AirChandler/pxt-arcade-RPi-smart-shield/cmsis_core/docs/Core/html/CMSIS_TZ_files.png

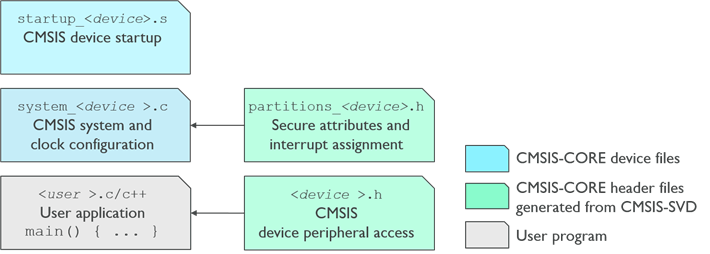
cmsis_core/docs/Core/html/CMSIS_TZ_files.png
