AirChandler/pxt-arcade-RPi-smart-shield/cmsis_core/docs/Core/html/SimpleUseCase.png

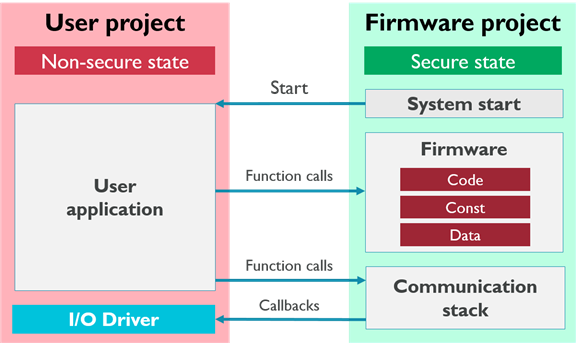
cmsis_core/docs/Core/html/SimpleUseCase.png
