AirChandler/pxt-arcade-RPi-smart-shield/cmsis_core/docs/DAP/html/CMSIS_DAP_SWStack.png

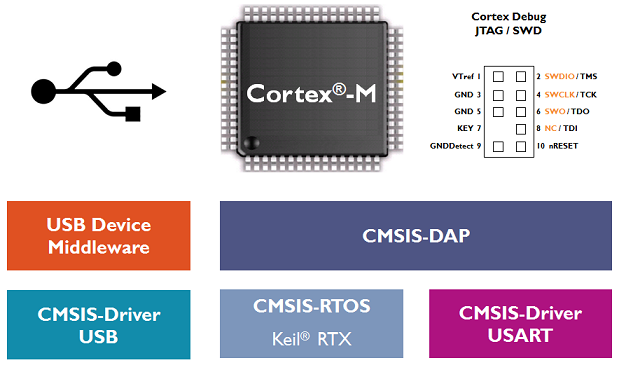
cmsis_core/docs/DAP/html/CMSIS_DAP_SWStack.png
