AirChandler/pxt-arcade-RPi-smart-shield/cmsis_core/docs/DAP/html/MDK_Flash.png

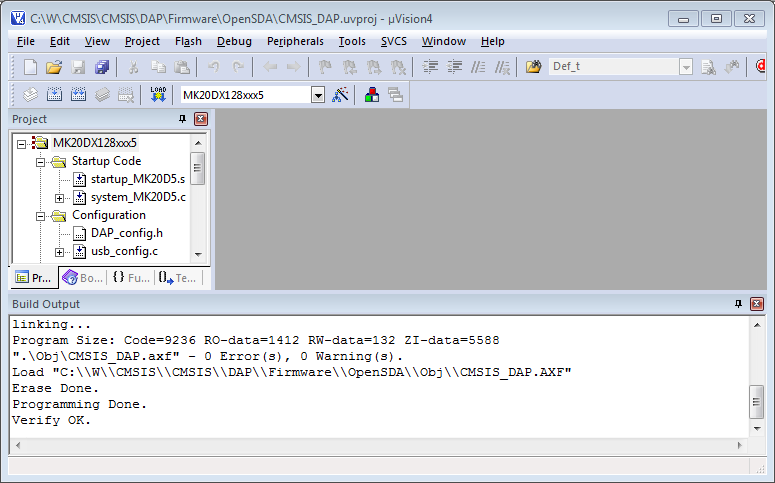
cmsis_core/docs/DAP/html/MDK_Flash.png
