AirChandler/pxt-arcade-RPi-smart-shield/cmsis_core/docs/DAP/html/RTE.png

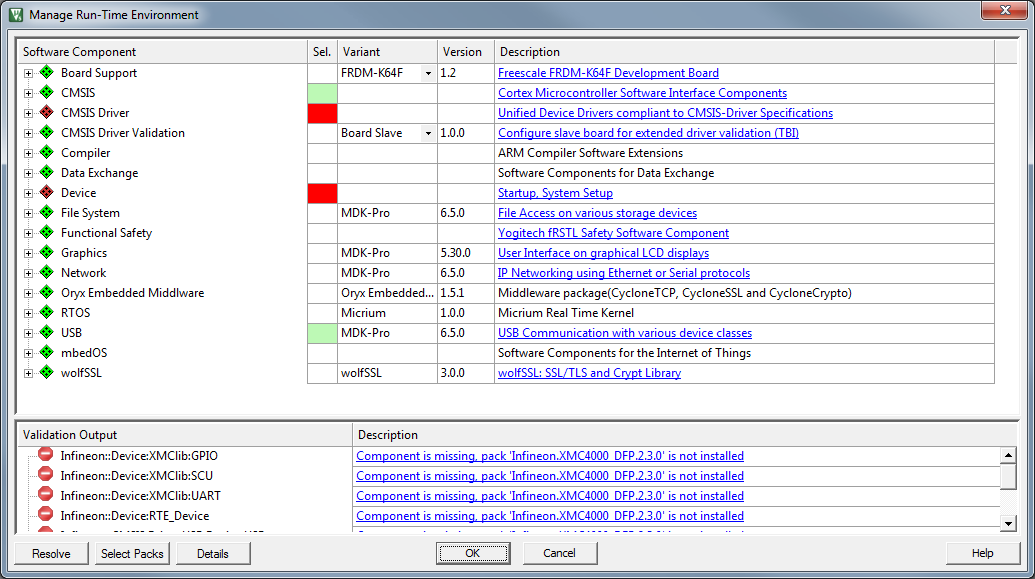
cmsis_core/docs/DAP/html/RTE.png
