AirChandler/pxt-arcade-RPi-smart-shield/cmsis_core/docs/Driver/html/driver_sai_i2s.png

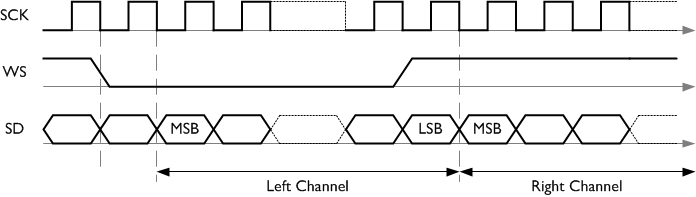
cmsis_core/docs/Driver/html/driver_sai_i2s.png
