AirChandler/pxt-arcade-RPi-smart-shield/cmsis_core/docs/Driver/html/I2C_BlockDiagram.png

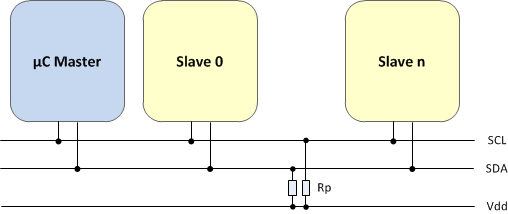
cmsis_core/docs/Driver/html/I2C_BlockDiagram.png
