AirChandler/pxt-arcade-RPi-smart-shield/cmsis_core/docs/Driver/html/msc_inline_mscgraph_2.png

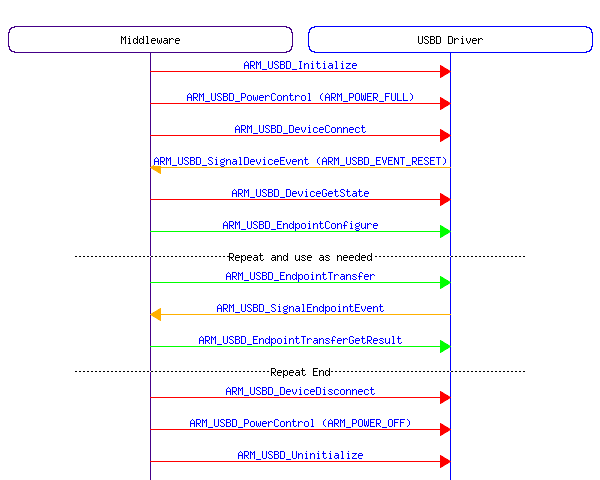
cmsis_core/docs/Driver/html/msc_inline_mscgraph_2.png
