AirChandler/pxt-arcade-RPi-smart-shield/cmsis_core/docs/Driver/html/NAND_Schematics.png

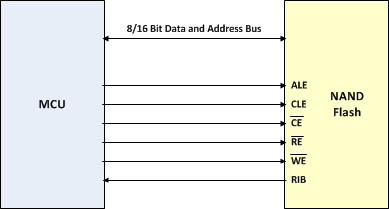
cmsis_core/docs/Driver/html/NAND_Schematics.png
