AirChandler/pxt-arcade-RPi-smart-shield/cmsis_core/docs/Driver/html/Non_blocking_transmit_small.png

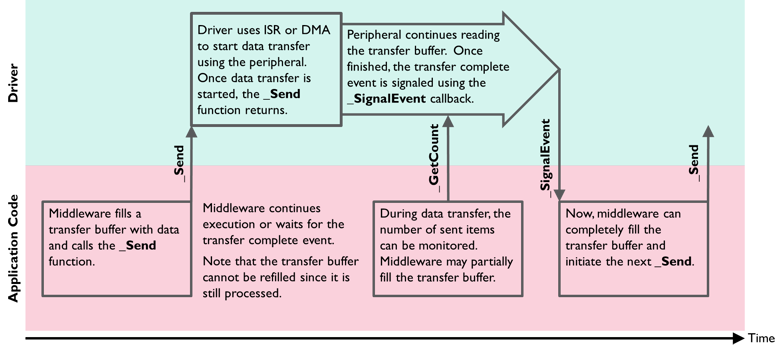
cmsis_core/docs/Driver/html/Non_blocking_transmit_small.png
