AirChandler/pxt-arcade-RPi-smart-shield/cmsis_core/docs/Driver/html/SAI_Schematics.png

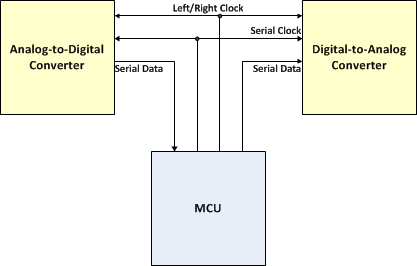
cmsis_core/docs/Driver/html/SAI_Schematics.png
