AirChandler/pxt-arcade-RPi-smart-shield/cmsis_core/docs/Driver/html/SD_4BitBusMode.png

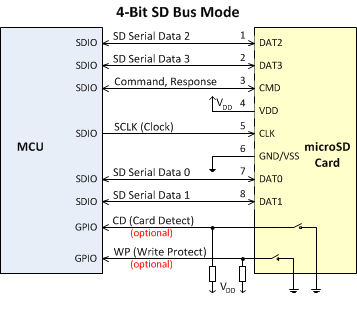
cmsis_core/docs/Driver/html/SD_4BitBusMode.png
