AirChandler/pxt-arcade-RPi-smart-shield/cmsis_core/docs/Driver/html/SPI_BusMode.png

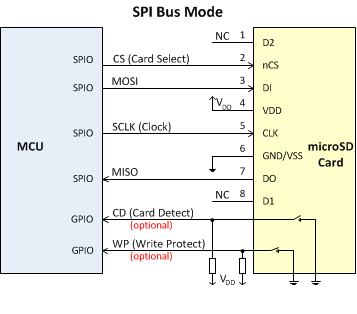
cmsis_core/docs/Driver/html/SPI_BusMode.png
