AirChandler/pxt-arcade-RPi-smart-shield/cmsis_core/docs/Driver/html/SPI_Master3Slaves.png

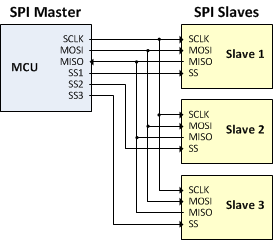
cmsis_core/docs/Driver/html/SPI_Master3Slaves.png
