AirChandler/pxt-arcade-RPi-smart-shield/cmsis_core/docs/Driver/html/storage_sw_stack.png

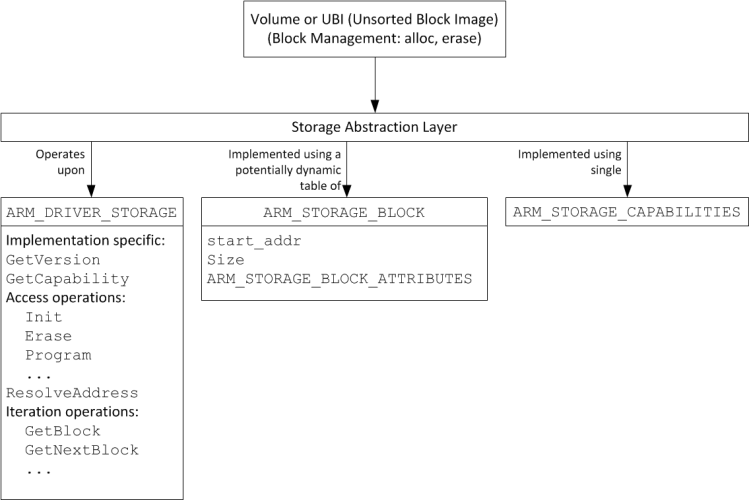
cmsis_core/docs/Driver/html/storage_sw_stack.png
