AirChandler/pxt-arcade-RPi-smart-shield/cmsis_core/docs/Driver/html/USB_Schematics.png

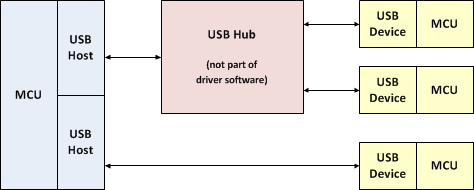
cmsis_core/docs/Driver/html/USB_Schematics.png
