AirChandler/pxt-arcade-RPi-smart-shield/cmsis_core/docs/Driver/html/WiFi.png

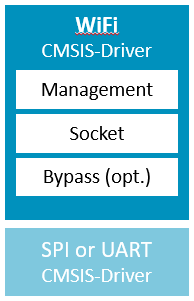
cmsis_core/docs/Driver/html/WiFi.png
