AirChandler/pxt-arcade-RPi-smart-shield/cmsis_core/docs/DSP/html/Biquad.gif

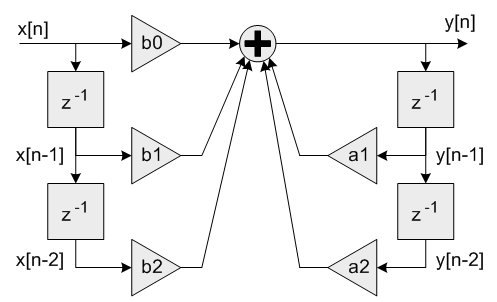
cmsis_core/docs/DSP/html/Biquad.gif
