AirChandler/pxt-arcade-RPi-smart-shield/cmsis_core/docs/DSP/html/BiquadPostshift.gif

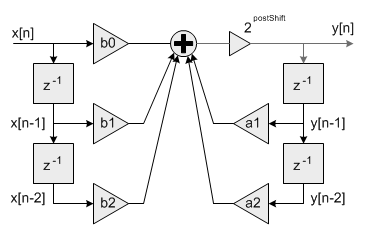
cmsis_core/docs/DSP/html/BiquadPostshift.gif
