AirChandler/pxt-arcade-RPi-smart-shield/cmsis_core/docs/DSP/html/FFTBinInput.gif

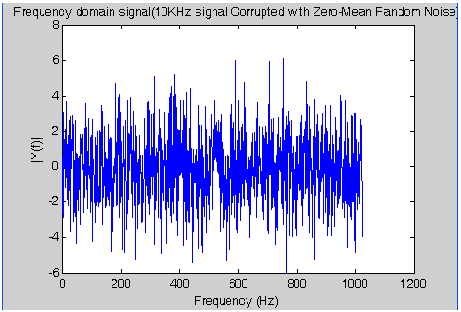
cmsis_core/docs/DSP/html/FFTBinInput.gif
