AirChandler/pxt-arcade-RPi-smart-shield/cmsis_core/docs/DSP/html/FIRLPF_coeffs.gif

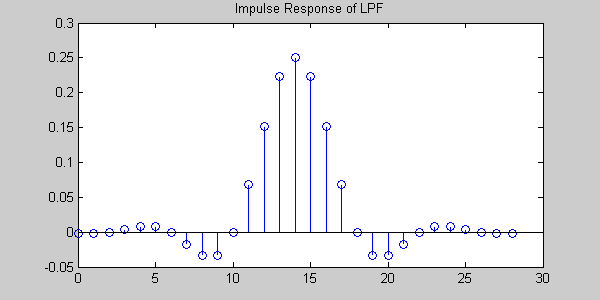
cmsis_core/docs/DSP/html/FIRLPF_coeffs.gif
