AirChandler/pxt-arcade-RPi-smart-shield/cmsis_core/docs/DSP/html/FIRLPF_output.gif

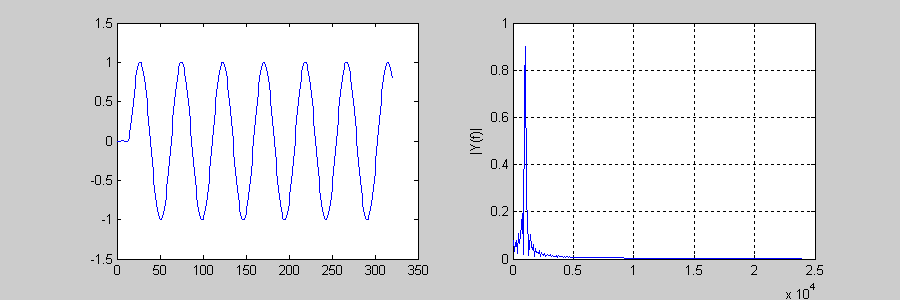
cmsis_core/docs/DSP/html/FIRLPF_output.gif
