AirChandler/pxt-arcade-RPi-smart-shield/cmsis_core/docs/DSP/html/FIRLPF_response.gif

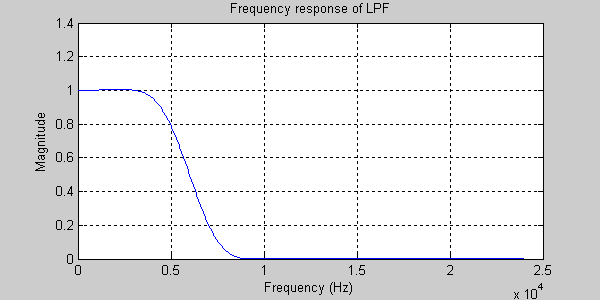
cmsis_core/docs/DSP/html/FIRLPF_response.gif
