AirChandler/pxt-arcade-RPi-smart-shield/cmsis_core/docs/DSP/html/GEQ_allbandresponse.gif

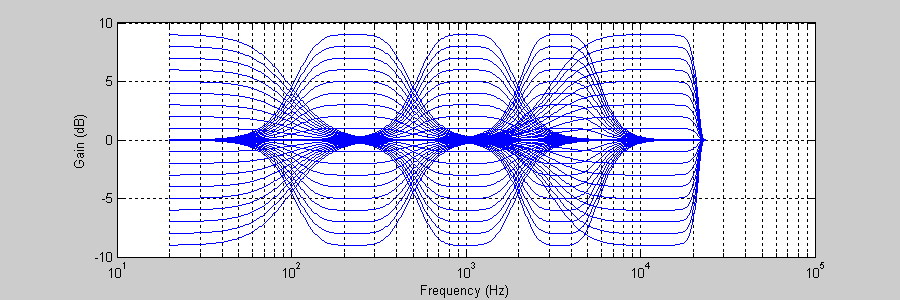
cmsis_core/docs/DSP/html/GEQ_allbandresponse.gif
