AirChandler/pxt-arcade-RPi-smart-shield/cmsis_core/docs/DSP/html/GEQ_bandresponse.gif

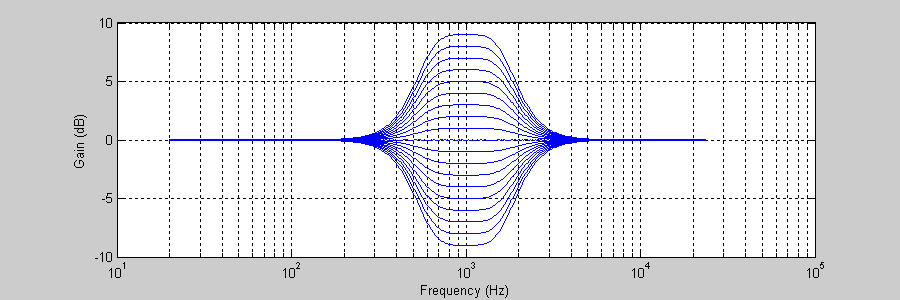
cmsis_core/docs/DSP/html/GEQ_bandresponse.gif
