AirChandler/pxt-arcade-RPi-smart-shield/cmsis_core/docs/DSP/html/IIRLattice.gif

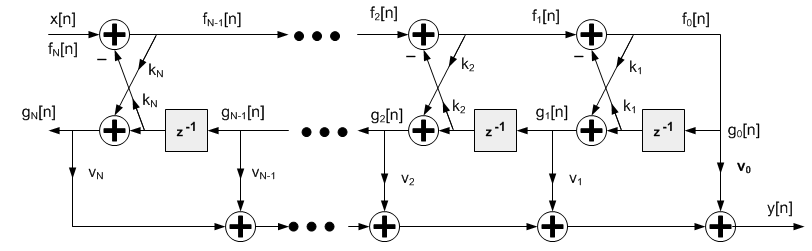
cmsis_core/docs/DSP/html/IIRLattice.gif
