AirChandler/pxt-arcade-RPi-smart-shield/cmsis_core/docs/DSP/html/MatrixInverse.gif

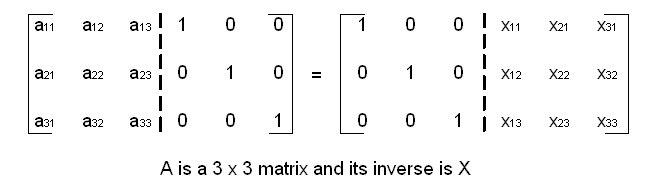
cmsis_core/docs/DSP/html/MatrixInverse.gif
