AirChandler/pxt-arcade-RPi-smart-shield/cmsis_core/docs/DSP/html/park.gif

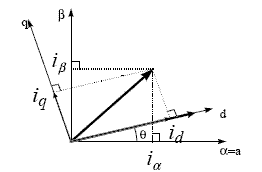
cmsis_core/docs/DSP/html/park.gif
