AirChandler/pxt-arcade-RPi-smart-shield/cmsis_core/docs/DSP/html/RFFTQ15.gif

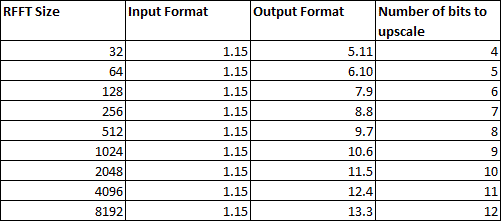
cmsis_core/docs/DSP/html/RFFTQ15.gif
