AirChandler/pxt-arcade-RPi-smart-shield/cmsis_core/docs/DSP/html/Variance.gif

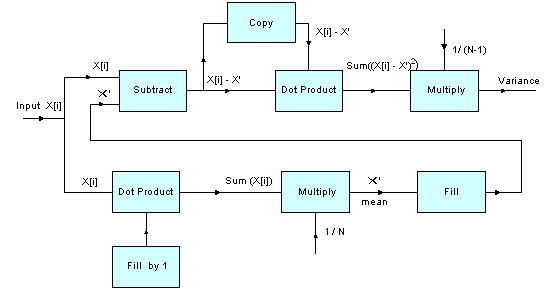
cmsis_core/docs/DSP/html/Variance.gif
