AirChandler/pxt-arcade-RPi-smart-shield/cmsis_core/docs/NN/html/CIFAR10_CNN.gif

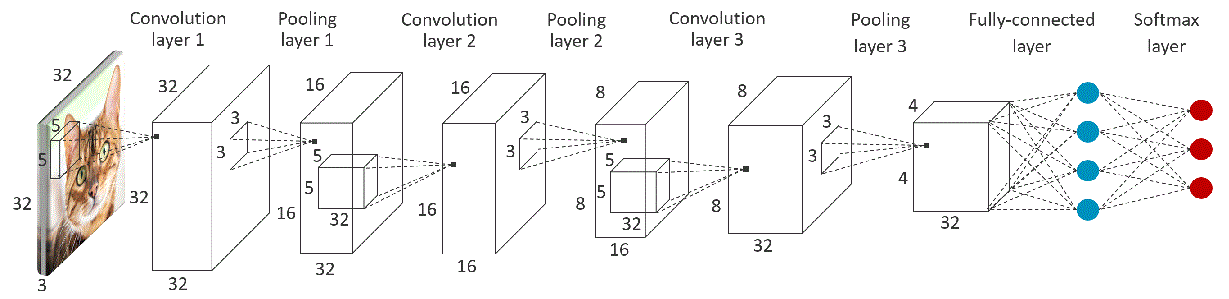
cmsis_core/docs/NN/html/CIFAR10_CNN.gif
