AirChandler/pxt-arcade-RPi-smart-shield/cmsis_core/docs/NN/html/GRU.gif

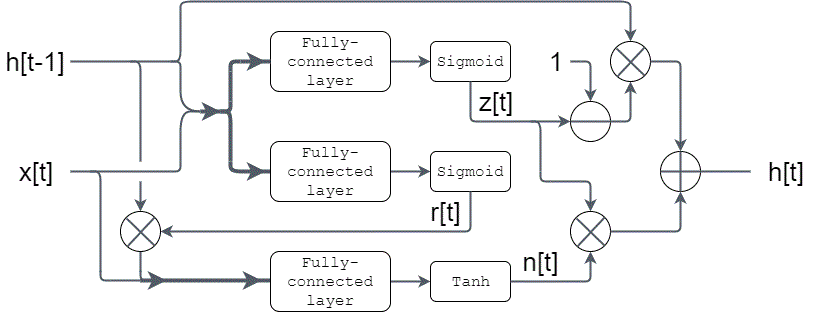
cmsis_core/docs/NN/html/GRU.gif
