AirChandler/pxt-arcade-RPi-smart-shield/cmsis_core/docs/Pack/html/api.png

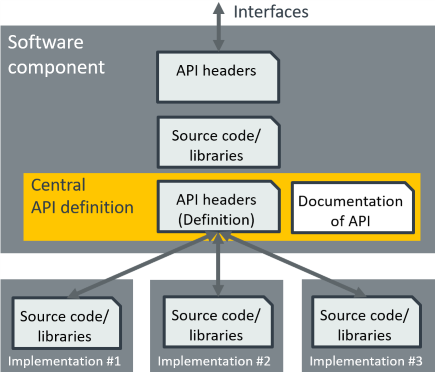
cmsis_core/docs/Pack/html/api.png
