AirChandler/pxt-arcade-RPi-smart-shield/cmsis_core/docs/Pack/html/BSPBundleDisplay.png

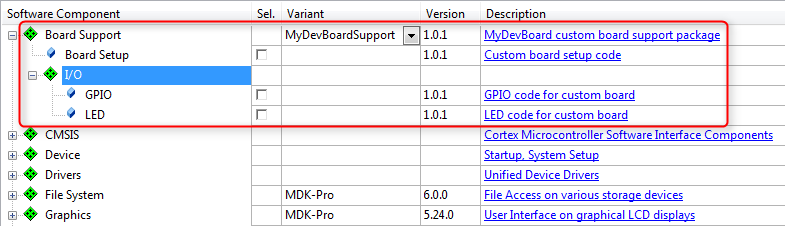
cmsis_core/docs/Pack/html/BSPBundleDisplay.png
