AirChandler/pxt-arcade-RPi-smart-shield/cmsis_core/docs/Pack/html/ConditionsDisplay.png

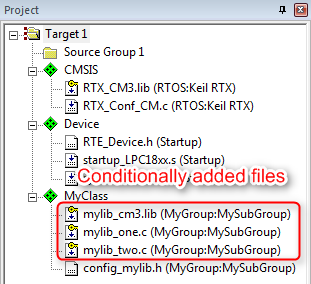
cmsis_core/docs/Pack/html/ConditionsDisplay.png
