AirChandler/pxt-arcade-RPi-smart-shield/cmsis_core/docs/Pack/html/DFPFlow.png

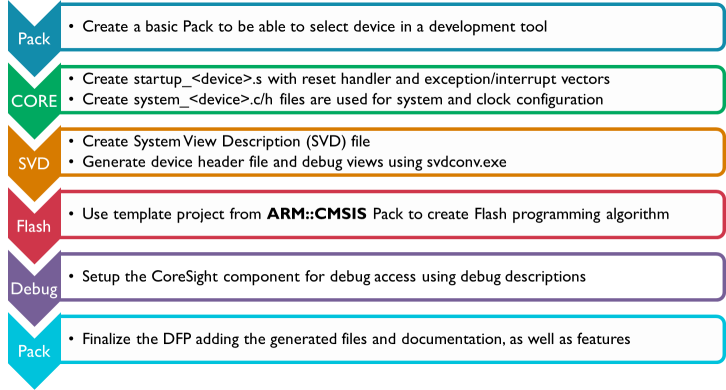
cmsis_core/docs/Pack/html/DFPFlow.png
