AirChandler/pxt-arcade-RPi-smart-shield/cmsis_core/docs/Pack/html/ExampleDisplay.png

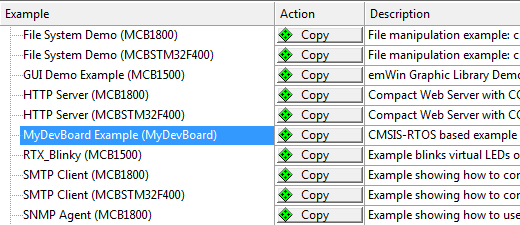
cmsis_core/docs/Pack/html/ExampleDisplay.png
