AirChandler/pxt-arcade-RPi-smart-shield/cmsis_core/docs/Pack/html/FlashProgram.png

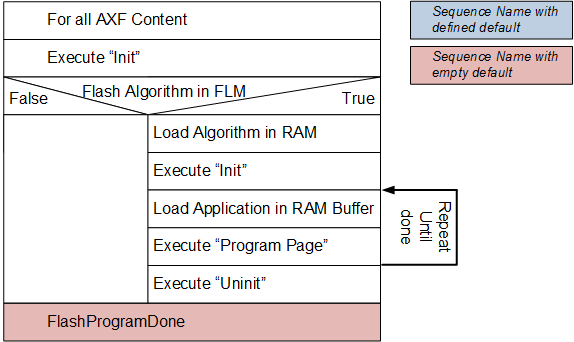
cmsis_core/docs/Pack/html/FlashProgram.png
