AirChandler/pxt-arcade-RPi-smart-shield/cmsis_core/docs/Pack/html/FPATargetOptions.png

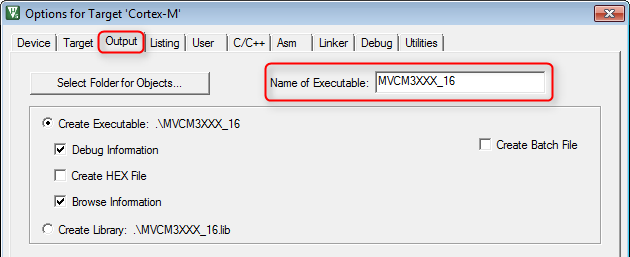
cmsis_core/docs/Pack/html/FPATargetOptions.png
