AirChandler/pxt-arcade-RPi-smart-shield/cmsis_core/docs/Pack/html/MVCM3SpecTable.png

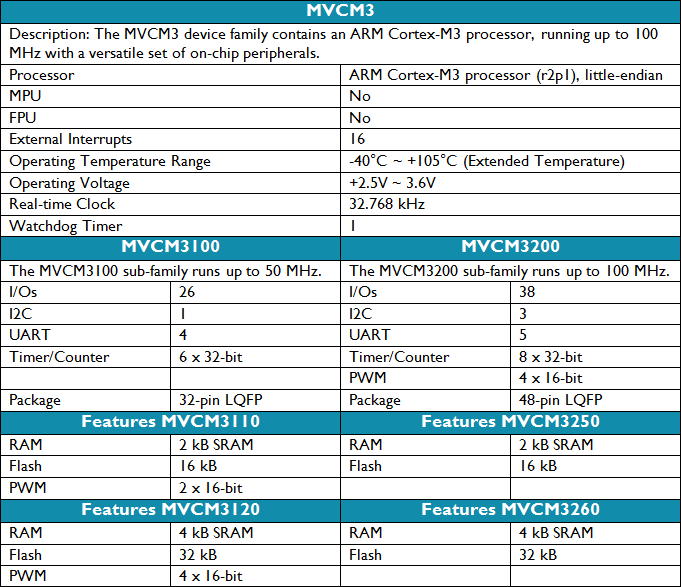
cmsis_core/docs/Pack/html/MVCM3SpecTable.png
