AirChandler/pxt-arcade-RPi-smart-shield/cmsis_core/docs/Pack/html/PDSC_Example_top.png

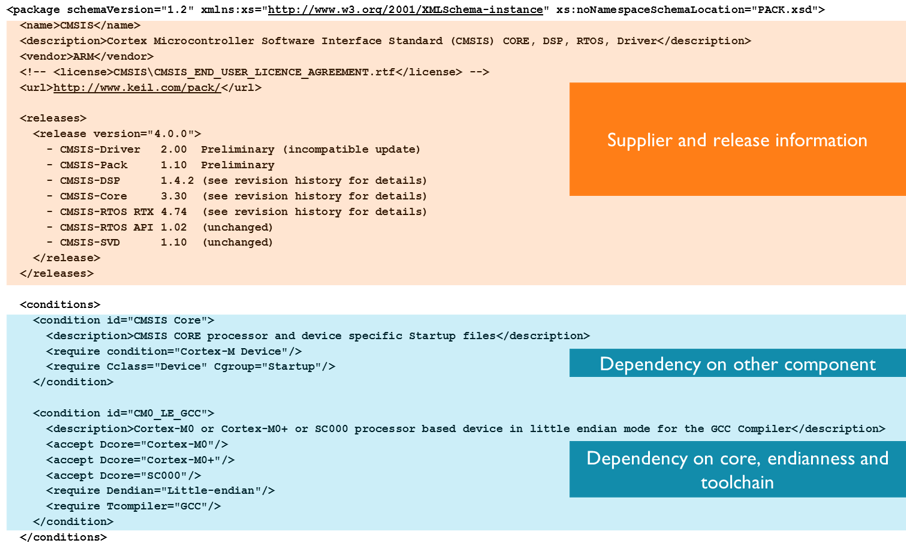
cmsis_core/docs/Pack/html/PDSC_Example_top.png
