AirChandler/pxt-arcade-RPi-smart-shield/cmsis_core/docs/Pack/html/Reset.png

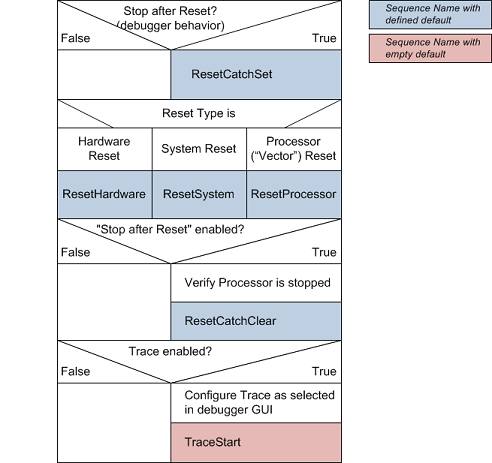
cmsis_core/docs/Pack/html/Reset.png
