AirChandler/pxt-arcade-RPi-smart-shield/cmsis_core/docs/Pack/html/StartupSystemFilesAdded.png

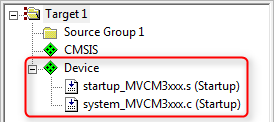
cmsis_core/docs/Pack/html/StartupSystemFilesAdded.png
