AirChandler/pxt-arcade-RPi-smart-shield/cmsis_core/docs/Pack/html/SVDIncluded.png

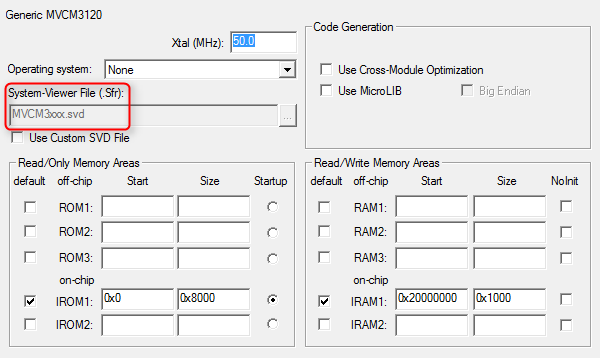
cmsis_core/docs/Pack/html/SVDIncluded.png
