AirChandler/pxt-arcade-RPi-smart-shield/cmsis_core/docs/Pack/html/VariantDisplay.png

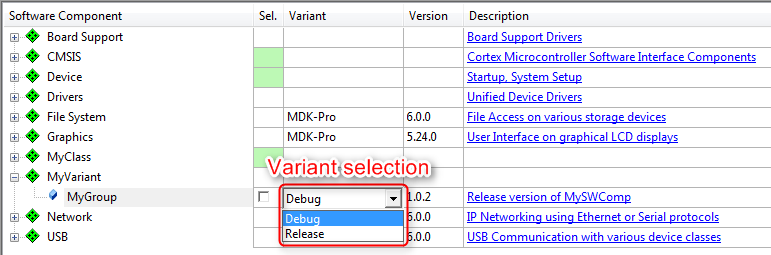
cmsis_core/docs/Pack/html/VariantDisplay.png
