AirChandler/pxt-arcade-RPi-smart-shield/cmsis_core/docs/RTOS2/html/config_wizard.png

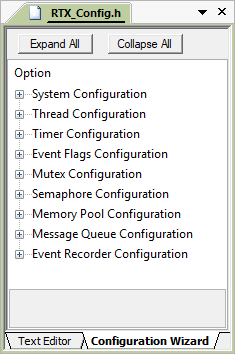
cmsis_core/docs/RTOS2/html/config_wizard.png
