AirChandler/pxt-arcade-RPi-smart-shield/cmsis_core/docs/RTOS2/html/manage_rte_output.png

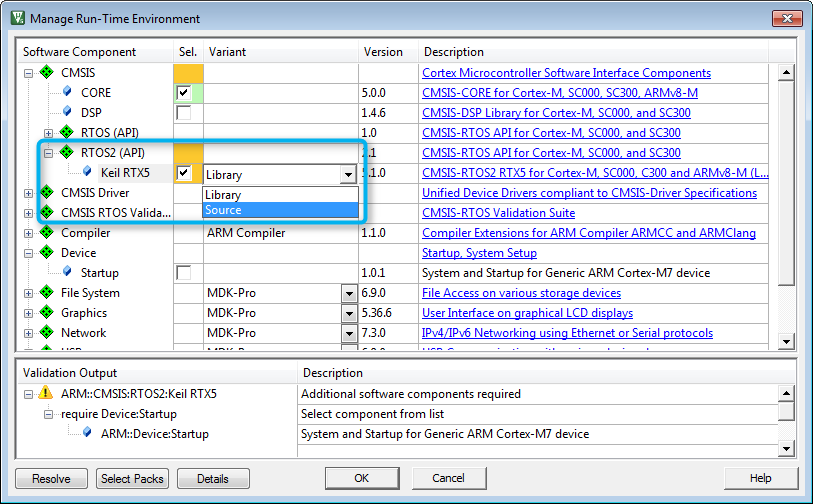
cmsis_core/docs/RTOS2/html/manage_rte_output.png
