AirChandler/pxt-arcade-RPi-smart-shield/cmsis_core/docs/RTOS2/html/MemAllocGlob.png

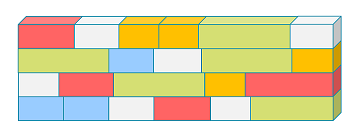
cmsis_core/docs/RTOS2/html/MemAllocGlob.png
