AirChandler/pxt-arcade-RPi-smart-shield/cmsis_core/docs/RTOS2/html/PC-Lint.png

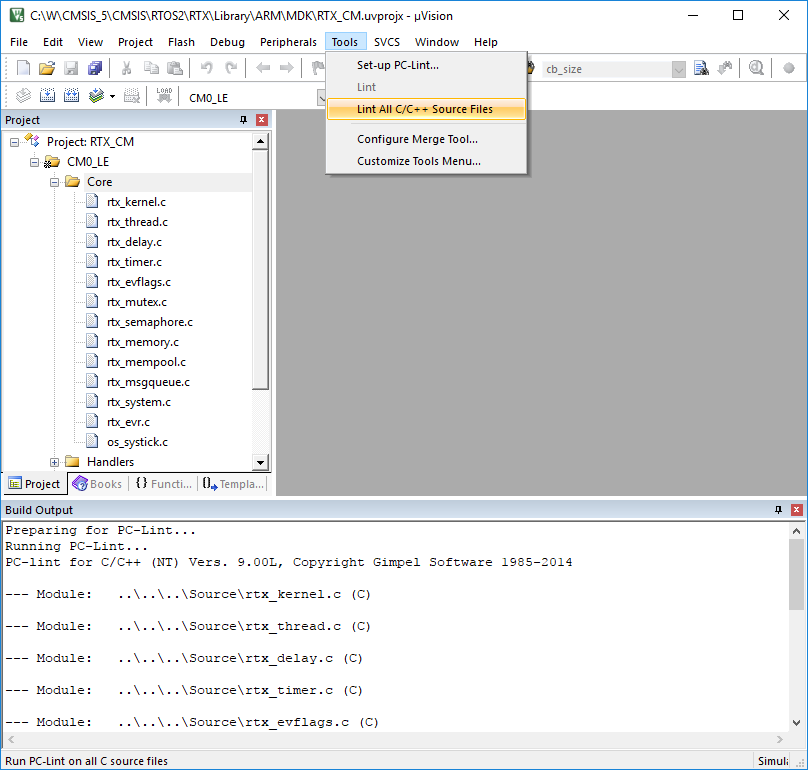
cmsis_core/docs/RTOS2/html/PC-Lint.png
