AirChandler/pxt-arcade-RPi-smart-shield/cmsis_core/docs/RTOS2/html/project_window.png

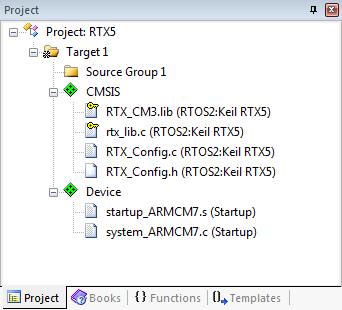
cmsis_core/docs/RTOS2/html/project_window.png
