AirChandler/pxt-arcade-RPi-smart-shield/cmsis_core/docs/RTOS2/html/simple_signal.png

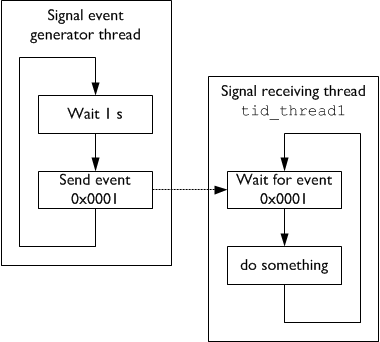
cmsis_core/docs/RTOS2/html/simple_signal.png
