AirChandler/pxt-arcade-RPi-smart-shield/cmsis_core/docs/RTOS/html/API_Structure.png

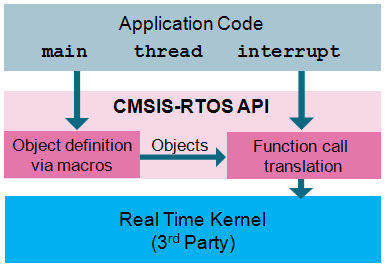
cmsis_core/docs/RTOS/html/API_Structure.png
