AirChandler/pxt-arcade-RPi-smart-shield/cmsis_core/docs/RTOS/html/CMSIS_RTOS_Files.png

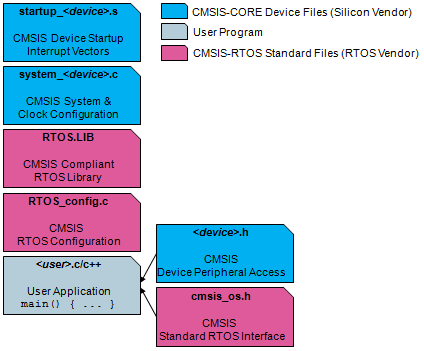
cmsis_core/docs/RTOS/html/CMSIS_RTOS_Files.png
