AirChandler/pxt-arcade-RPi-smart-shield/cmsis_core/docs/RTOS/html/config_wizard.png

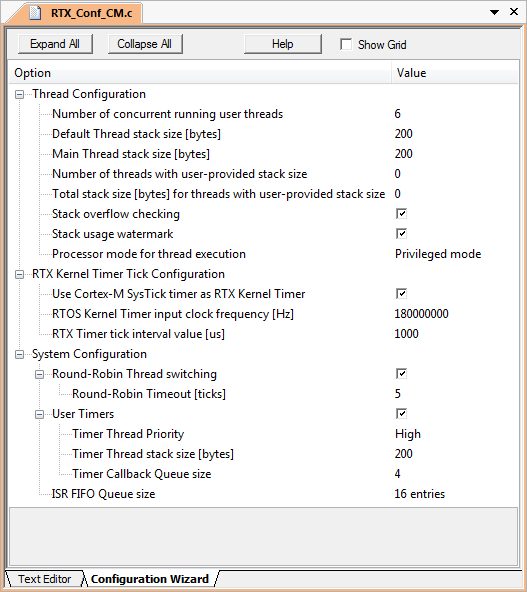
cmsis_core/docs/RTOS/html/config_wizard.png
