AirChandler/pxt-arcade-RPi-smart-shield/cmsis_core/docs/SVD/html/CMSIS_SVD_Schema_Gen.png

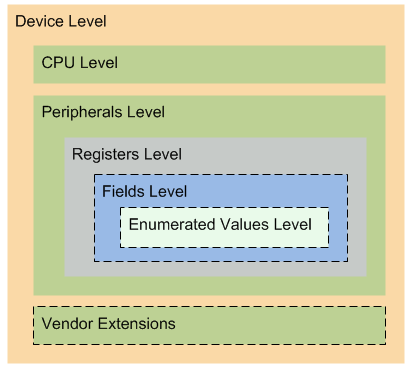
cmsis_core/docs/SVD/html/CMSIS_SVD_Schema_Gen.png
