AirChandler/pxt-arcade-RPi-smart-shield/cmsis_core/docs/Zone/html/AddMemoryBlock.png

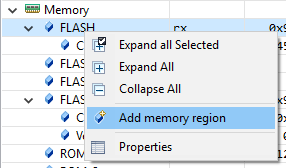
cmsis_core/docs/Zone/html/AddMemoryBlock.png
