AirChandler/pxt-arcade-RPi-smart-shield/cmsis_core/docs/Zone/html/DelMemoryRegion.png

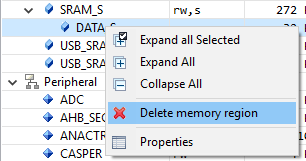
cmsis_core/docs/Zone/html/DelMemoryRegion.png
