AirChandler/pxt-arcade-RPi-smart-shield/cmsis_core/docs/Zone/html/hello_world_output.png

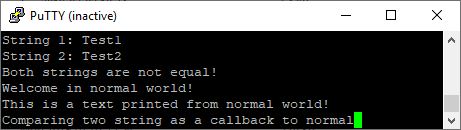
cmsis_core/docs/Zone/html/hello_world_output.png
