AirChandler/pxt-arcade-RPi-smart-shield/cmsis_core/docs/Zone/html/import_from_file.png

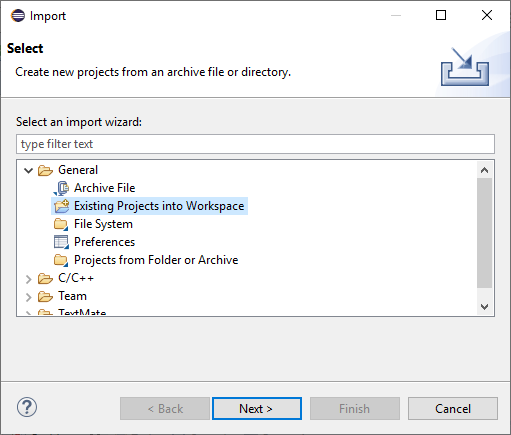
cmsis_core/docs/Zone/html/import_from_file.png
