AirChandler/pxt-arcade-RPi-smart-shield/cmsis_core/docs/Zone/html/import_projects.png

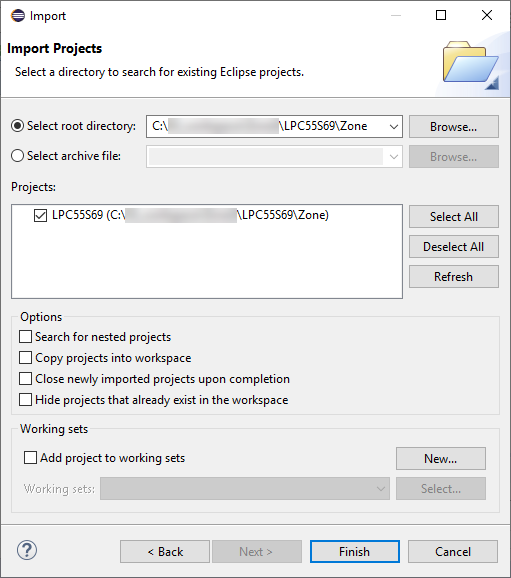
cmsis_core/docs/Zone/html/import_projects.png
