AirChandler/pxt-arcade-RPi-smart-shield/cmsis_core/docs/Zone/html/lpc55_resource_map.png

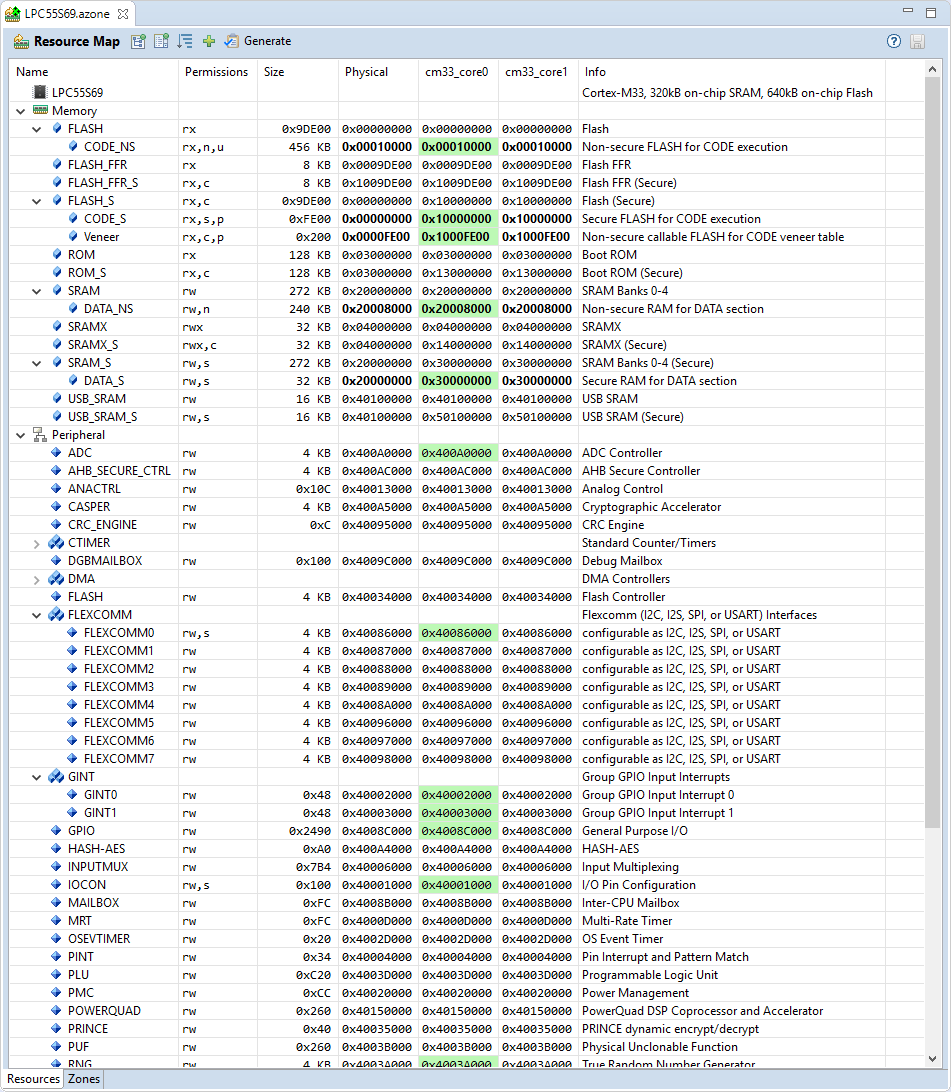
cmsis_core/docs/Zone/html/lpc55_resource_map.png
