AirChandler/pxt-arcade-RPi-smart-shield/cmsis_core/docs/Zone/html/lpc55_system_startup.png

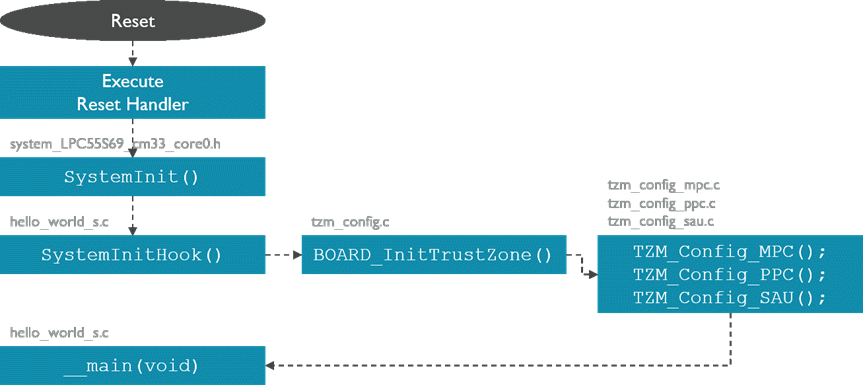
cmsis_core/docs/Zone/html/lpc55_system_startup.png
