AirChandler/pxt-arcade-RPi-smart-shield/cmsis_core/docs/Zone/html/mpu.png

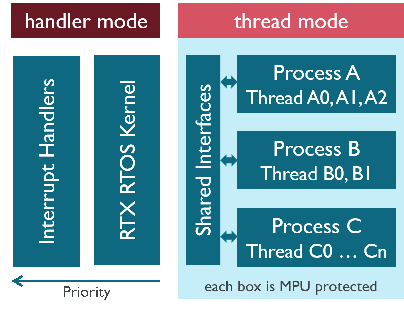
cmsis_core/docs/Zone/html/mpu.png
