AirChandler/pxt-arcade-RPi-smart-shield/cmsis_core/docs/Zone/html/NewZoneCM33_0.png

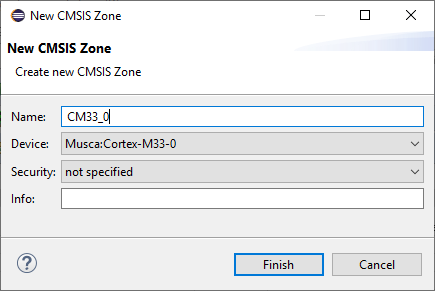
cmsis_core/docs/Zone/html/NewZoneCM33_0.png
