AirChandler/pxt-arcade-RPi-smart-shield/cmsis_core/docs/Zone/html/Partitioning_Hardware.png

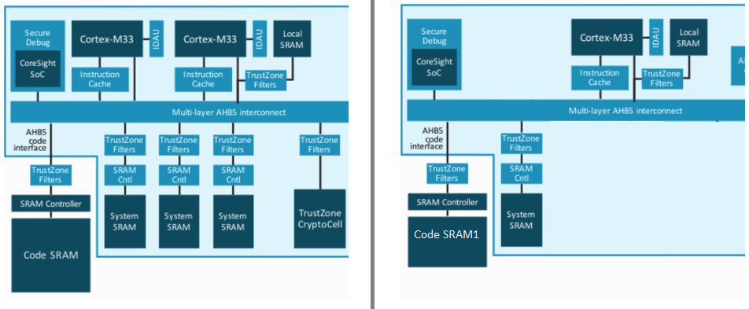
cmsis_core/docs/Zone/html/Partitioning_Hardware.png
