AirChandler/pxt-arcade-RPi-smart-shield/cmsis_core/docs/Zone/html/Partitioning_Workflow.png

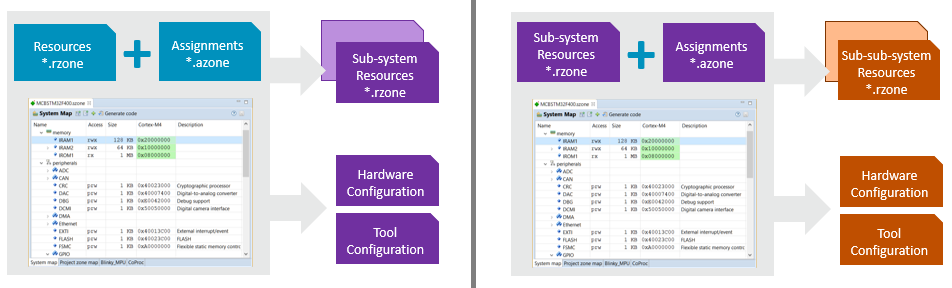
cmsis_core/docs/Zone/html/Partitioning_Workflow.png
