AirChandler/pxt-arcade-RPi-smart-shield/cmsis_core/docs/Zone/html/peripheral_properties.png

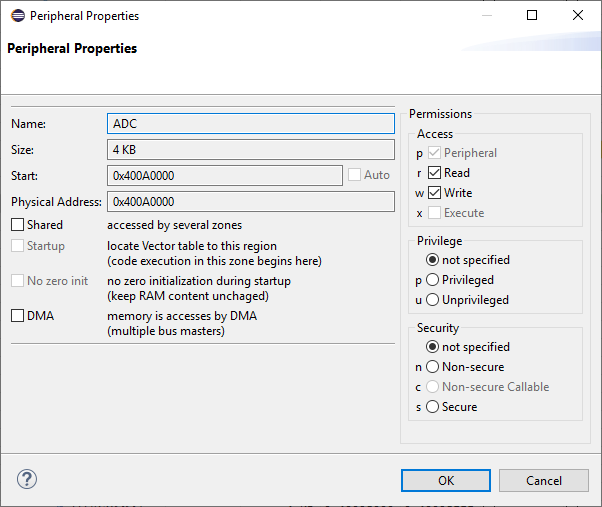
cmsis_core/docs/Zone/html/peripheral_properties.png
