AirChandler/pxt-arcade-RPi-smart-shield/cmsis_core/docs/Zone/html/res_prop.png

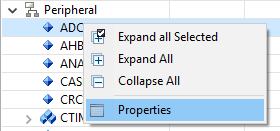
cmsis_core/docs/Zone/html/res_prop.png
