AirChandler/pxt-arcade-RPi-smart-shield/cmsis_core/docs/Zone/html/SpecifyRzoneFile.png

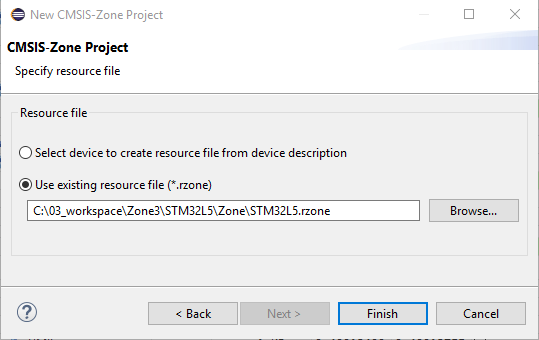
cmsis_core/docs/Zone/html/SpecifyRzoneFile.png
