AirChandler/pxt-arcade-RPi-smart-shield/cmsis_core/docs/Zone/html/STM32L5_zones.png

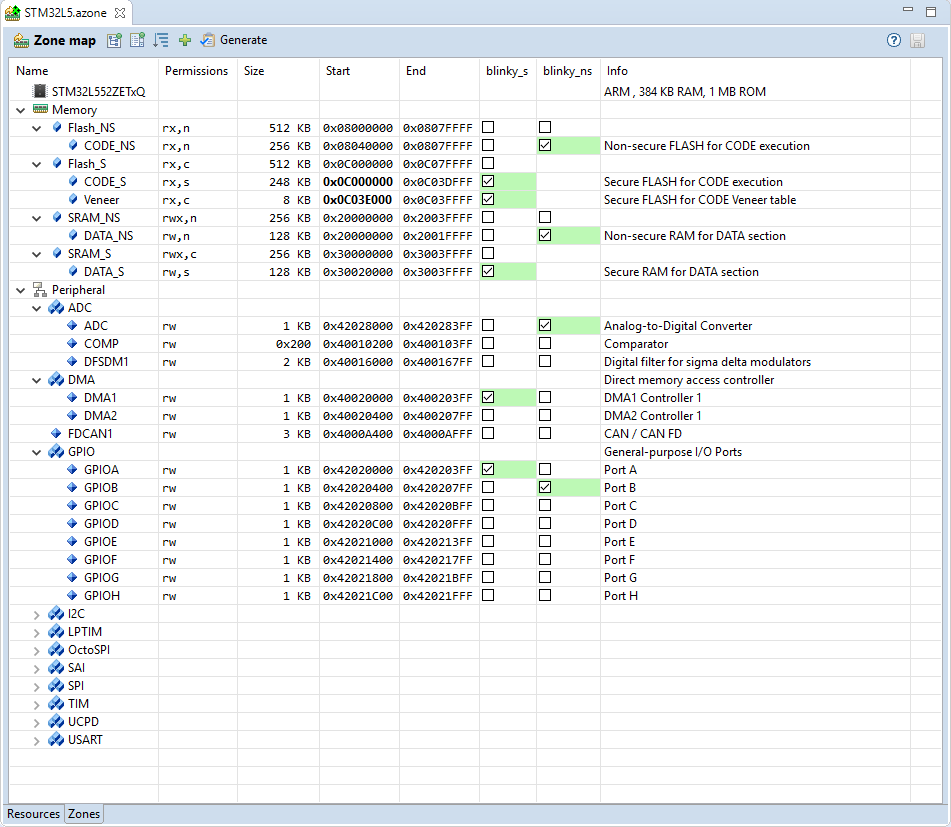
cmsis_core/docs/Zone/html/STM32L5_zones.png
