AirChandler/pxt-arcade-RPi-smart-shield/cmsis_core/docs/Zone/html/zone_map.png

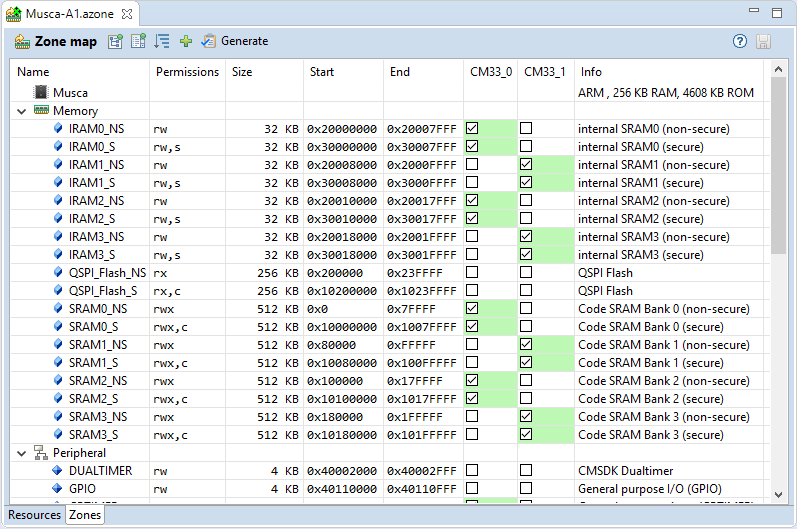
cmsis_core/docs/Zone/html/zone_map.png
