AirChandler/pxt-arcade-RPi-smart-shield/jacdac-c/jacdac/spec/images/jacdac-proto-timings.png

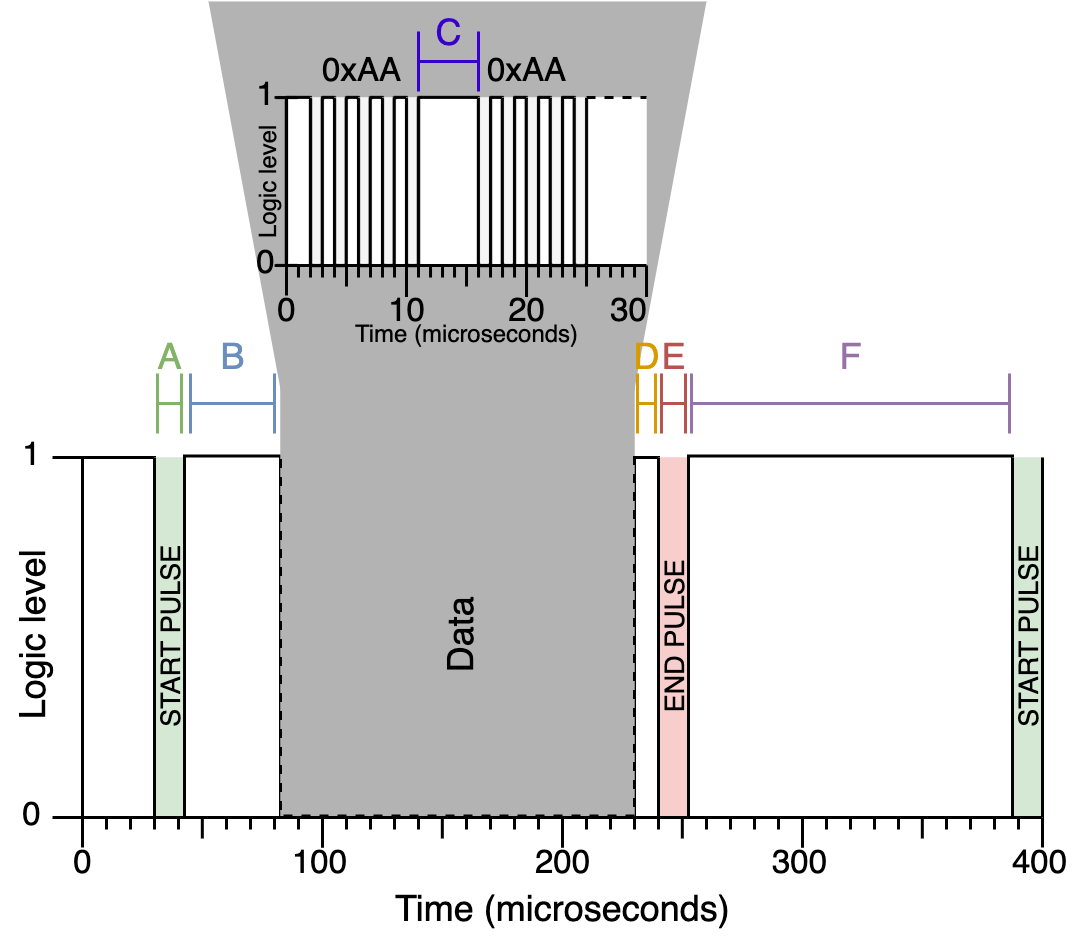
jacdac-c/jacdac/spec/images/jacdac-proto-timings.png
