AirChandler/pxt-arcade-RPi-smart-shield/jacdac-c/jacdac/spec/images/jacdac-stack-no-trans.png

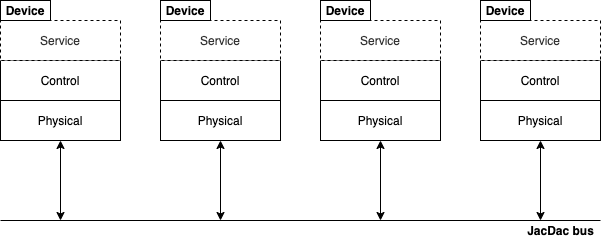
jacdac-c/jacdac/spec/images/jacdac-stack-no-trans.png
