AirChandler/pxt-arcade-RPi-smart-shield/jacdac-c/jacdac/spec/images/jacdac-state-diagram.png

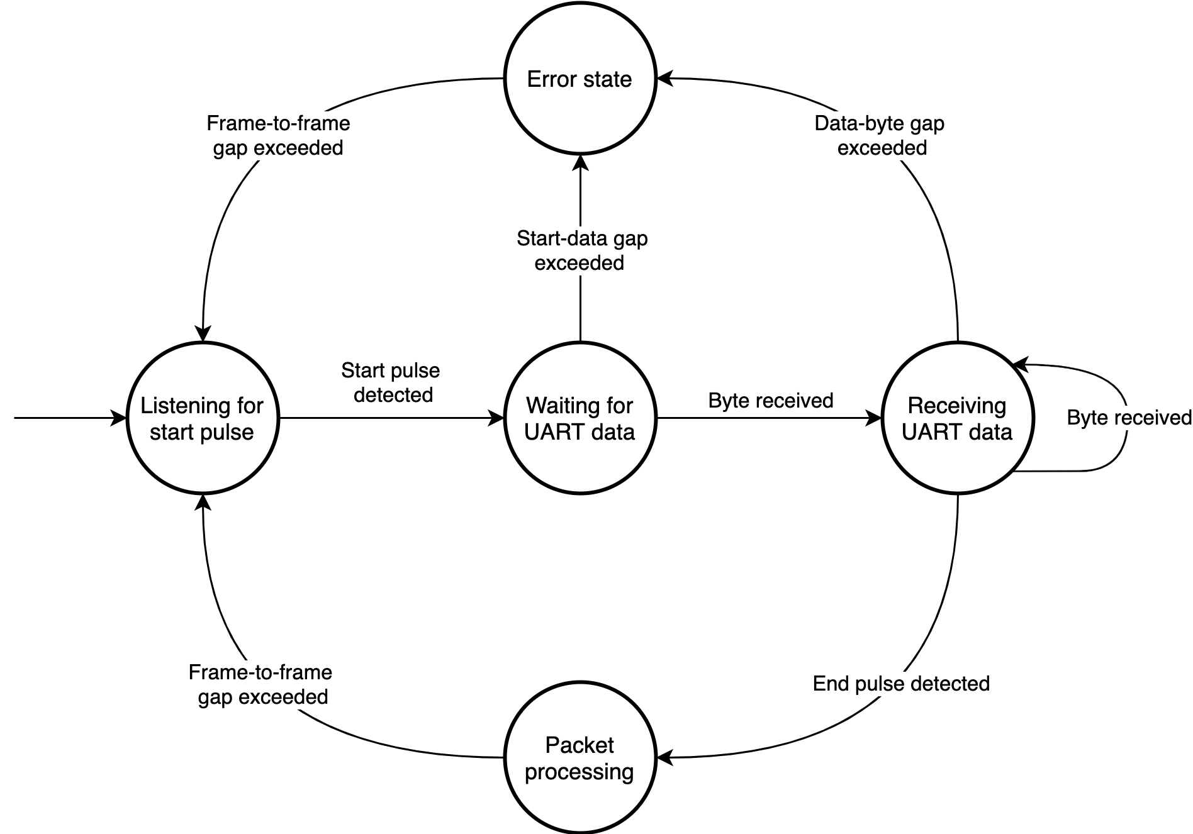
jacdac-c/jacdac/spec/images/jacdac-state-diagram.png
