AirChandler/pxt-arcade-RPi-smart-shield/cmsis_core/docs/Pack/html/component_files.png

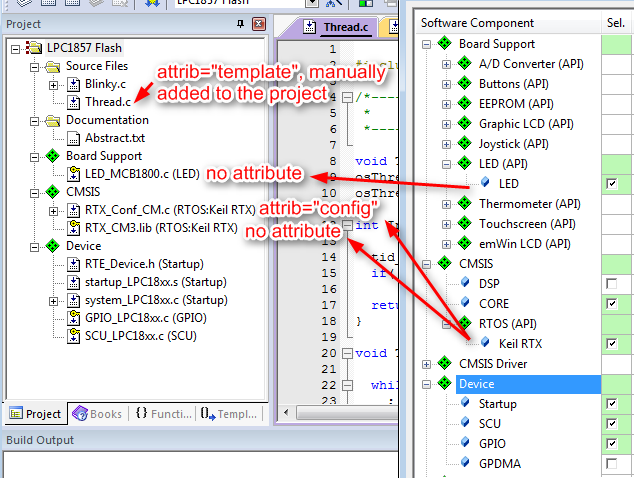
cmsis_core/docs/Pack/html/component_files.png
