AirChandler/pxt-arcade-RPi-smart-shield/cmsis_core/docs/Pack/html/Component_Instances.png

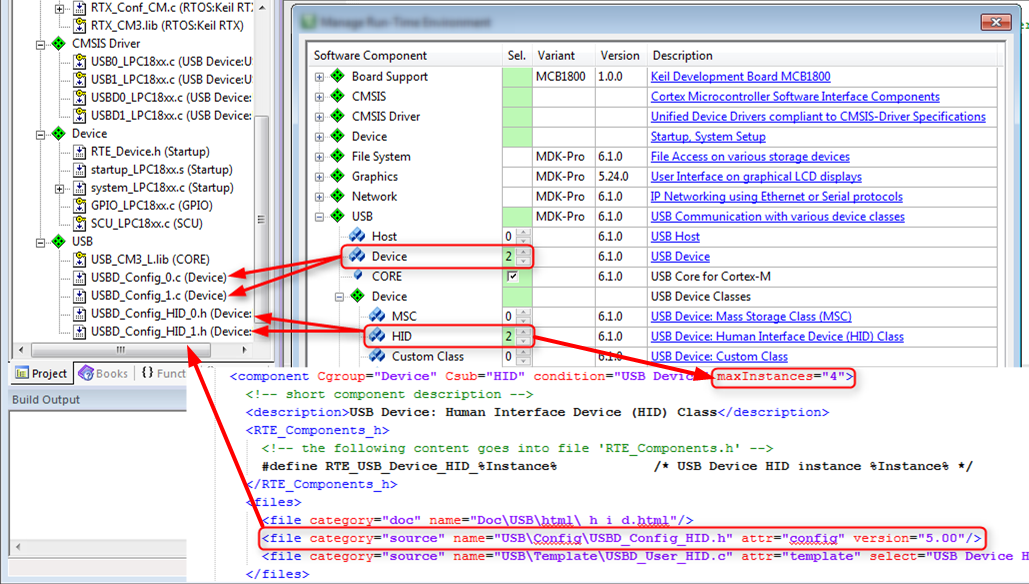
cmsis_core/docs/Pack/html/Component_Instances.png
