AirChandler/pxt-arcade-RPi-smart-shield/cmsis_core/docs/Pack/html/ComponentDisplay.png

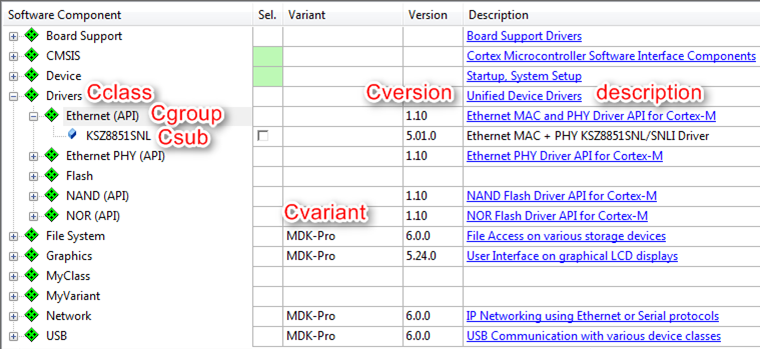
cmsis_core/docs/Pack/html/ComponentDisplay.png
