AirChandler/pxt-arcade-RPi-smart-shield/cmsis_core/docs/Pack/html/LocalInstallation.png

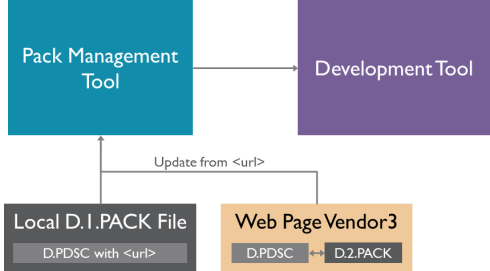
cmsis_core/docs/Pack/html/LocalInstallation.png
