AirChandler/pxt-arcade-RPi-smart-shield/cmsis_core/docs/Pack/html/PackCreateSteps.png

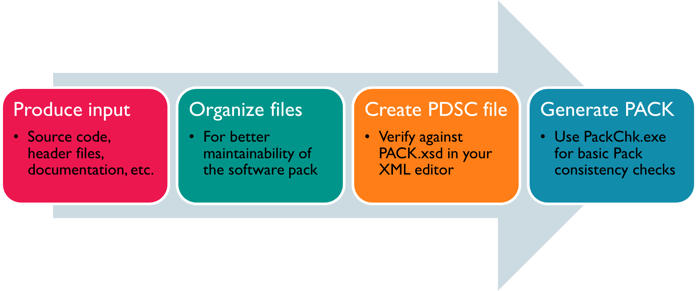
cmsis_core/docs/Pack/html/PackCreateSteps.png
