AirChandler/pxt-arcade-RPi-smart-shield/cmsis_core/docs/Pack/html/WebInstallation.png

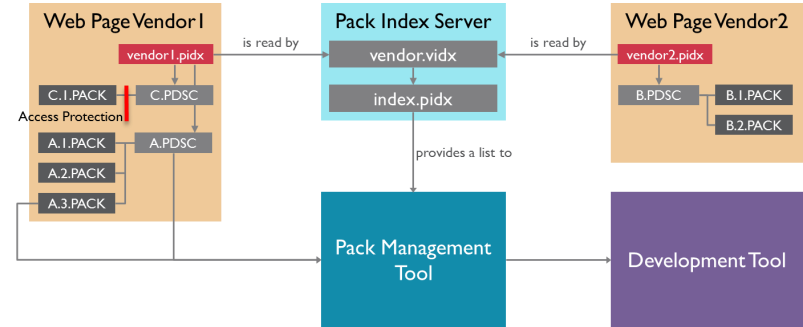
cmsis_core/docs/Pack/html/WebInstallation.png
