AirChandler/pxt-arcade-RPi-smart-shield/cmsis_core/docs/RTOS2/html/config_wizard_evtrecRTOSEvtFilterSetup.png

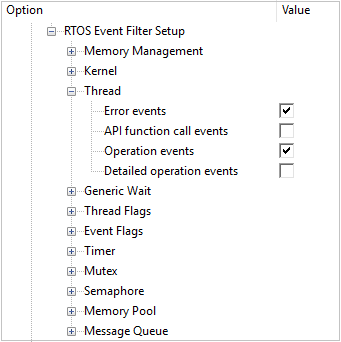
cmsis_core/docs/RTOS2/html/config_wizard_evtrecRTOSEvtFilterSetup.png
