AirChandler/pxt-arcade-RPi-smart-shield/cmsis_core/docs/RTOS2/html/KernelStackUsage.png

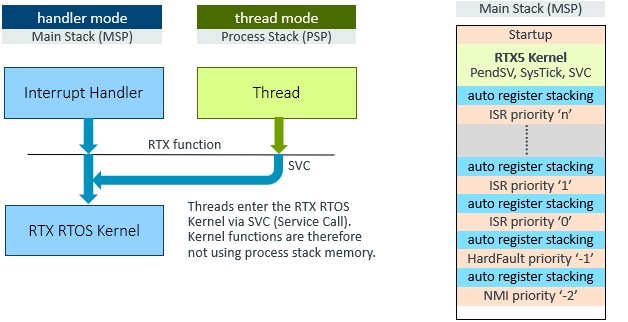
cmsis_core/docs/RTOS2/html/KernelStackUsage.png
