AirChandler/pxt-arcade-RPi-smart-shield/cmsis_core/docs/RTOS/html/stack_usage_watermark.png

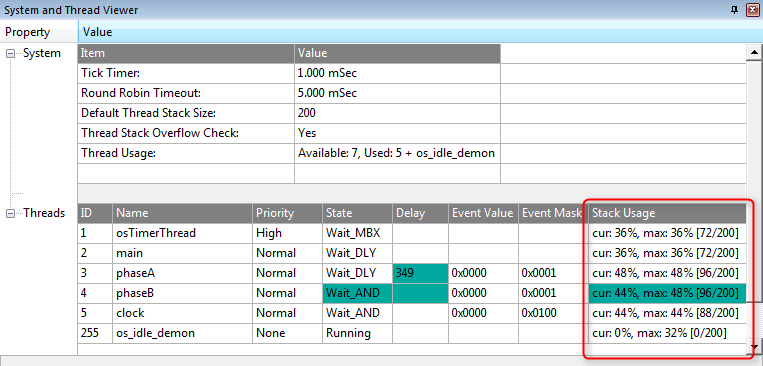
cmsis_core/docs/RTOS/html/stack_usage_watermark.png
