AirChandler/pxt-arcade-RPi-smart-shield/cmsis_core/docs/DAP/html/MDK_Validation.png

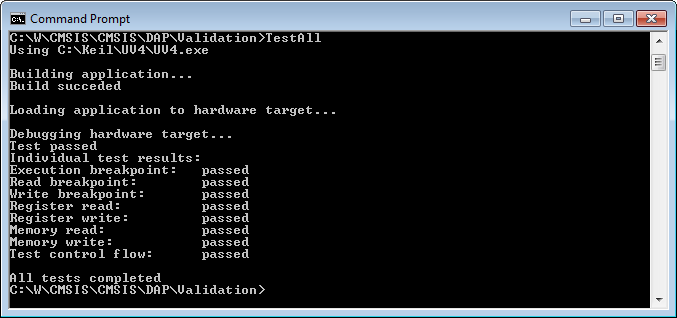
cmsis_core/docs/DAP/html/MDK_Validation.png
