AirChandler/pxt-arcade-RPi-smart-shield/cmsis_core/docs/Pack/html/FlashVerify.png

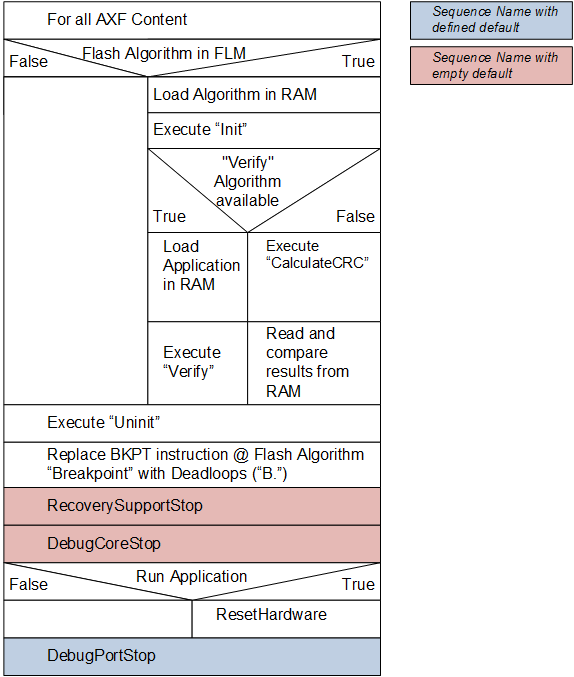
cmsis_core/docs/Pack/html/FlashVerify.png
