AirChandler/pxt-arcade-RPi-smart-shield/cmsis_core/docs/DAP/html/CMSIS_DAP_DEBUG_UNIT_ISO.png

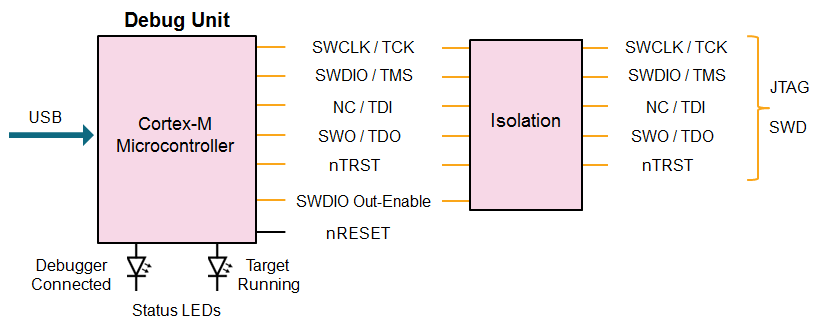
cmsis_core/docs/DAP/html/CMSIS_DAP_DEBUG_UNIT_ISO.png
