AirChandler/pxt-arcade-RPi-smart-shield/cmsis_core/docs/Pack/html/DebugConnect.png

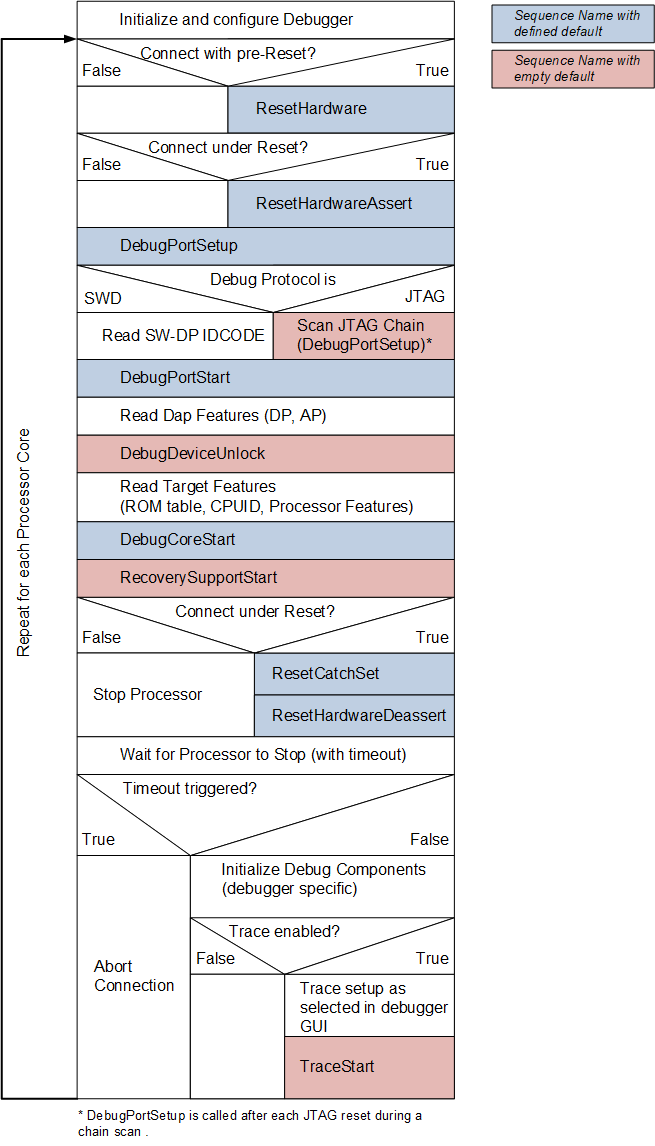
cmsis_core/docs/Pack/html/DebugConnect.png
