AirChandler/pxt-arcade-RPi-smart-shield/cmsis_core/docs/Pack/html/DebugDisconnect.png

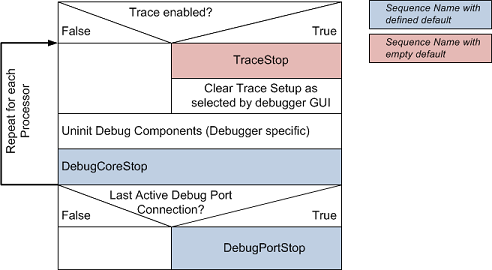
cmsis_core/docs/Pack/html/DebugDisconnect.png
